lpercifield/visualight/Hardware/dev/DIY/5Wled-mosfet.brd

## EAGLE design Hardware/dev/DIY/5Wled-mosfet.brd (2013-02-26)

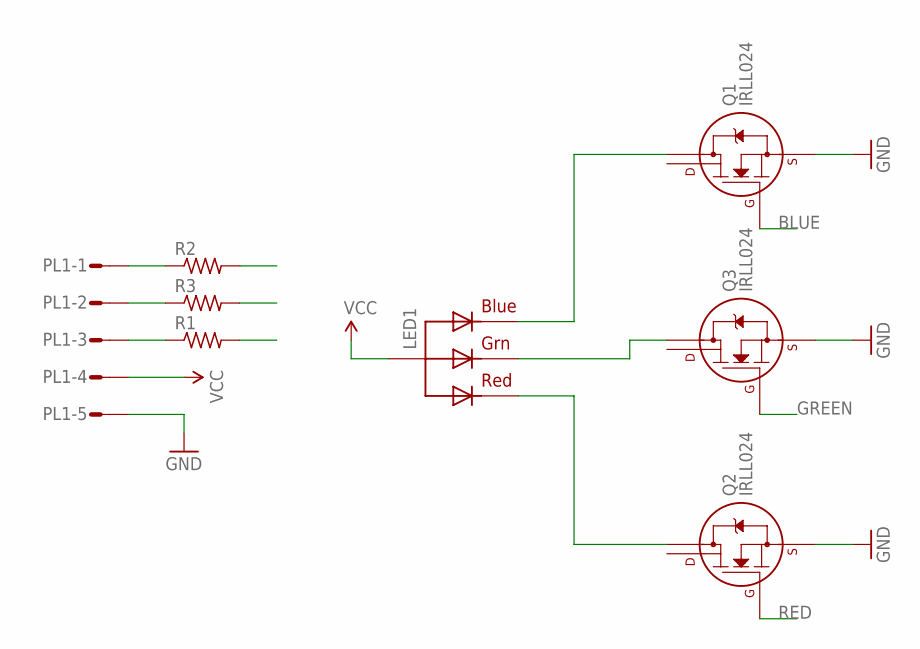
[picture p26: schematic 5Wled-mosfet.sch]

Parts:
LED1: RGBLED_CA4.5MM; 5WRGBLED
PL1: DF3-05R; DF3R-05
Q1, Q2, Q3: IRLL024; SOT-223
R1, R2, R3: R-US_0204/5; 0204/5

Connections:
BLUE: Q1.1 (G), R1.2
GND: PL1.5, Q1.3 (S), Q2.3 (S), Q3.3 (S)
GREEN: Q3.1 (G), R3.2
unnamed: LED1.1 (BLUE), Q1.2 (D1)
unnamed: LED1.3 (GREEN), Q3.2 (D1)
unnamed: LED1.2 (RED), Q2.2 (D1)
unnamed: PL1.1, R2.1
unnamed: PL1.2, R3.1
unnamed: PL1.3, R1.1
RED: Q2.1 (G), R2.2
VCC: LED1.4 (VCC), PL1.4

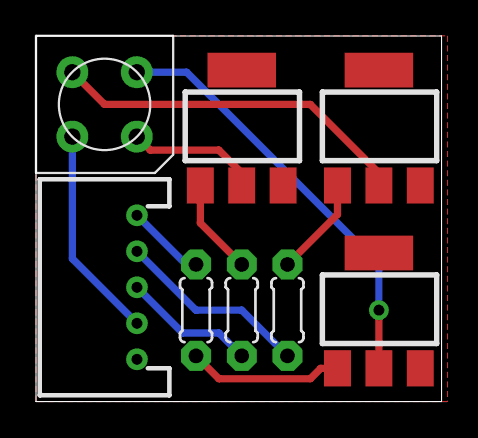
[picture p27: board 5Wled-mosfet.brd from above]

Board: 2 copper layers, 22.5 x 20.3 mm, 8 parts (0 on the bottom side), 11 nets.
