lpercifield/visualight/Hardware/dev/bulb/LEDdriverSFE_CREE.brd

## EAGLE design Hardware/dev/bulb/LEDdriverSFE_CREE.brd (2013-09-26)

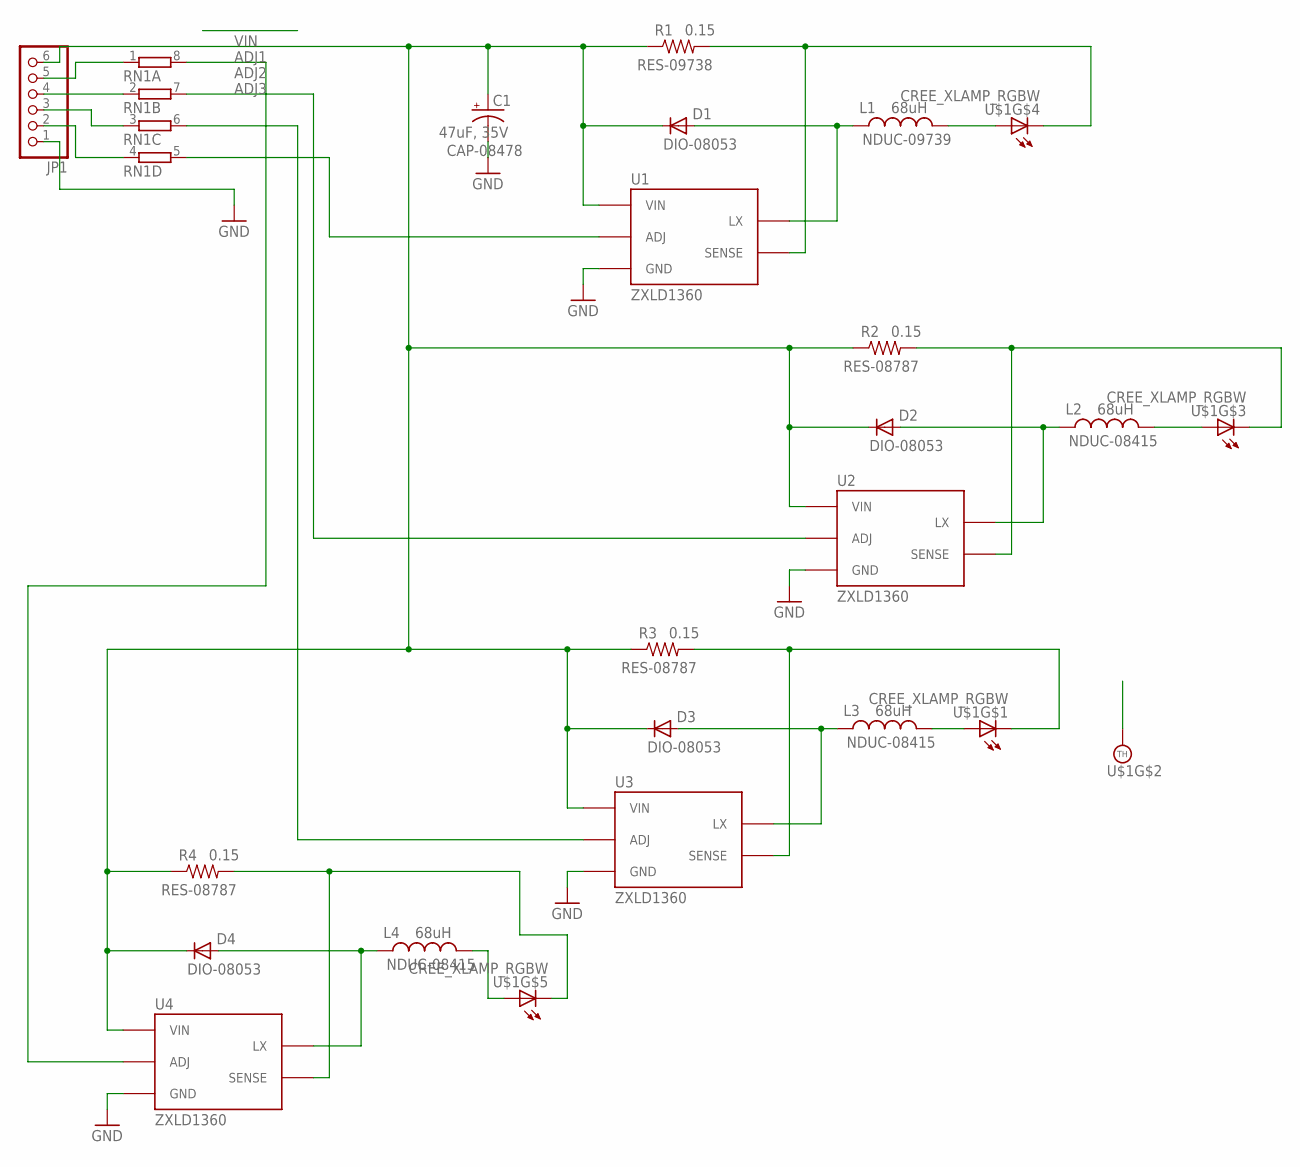
[picture p28: schematic LEDdriverSFE_CREE.sch]

Parts:
C1: 47uF, 35V; PANASONIC_D
D1, D2, D3, D4: MBRA140; SMA-DIODE
JP1: PINHD-1X6; 1X06
L1, L2, L3, L4: 68uH; CR75
R1, R2, R3, R4: 0.15; 0603-RES
RN1: 4R-NEXBV8V; EXBV8V
U1, U2, U3, U4: ZXLD1360; SOT23-5
U$1: CREE_XLAMP_RGBW; CREE_XLAMP_XML

Connections:
ADJ1: RN1.5 (2), U1.3 (ADJ)
ADJ2: RN1.7 (2), U2.3 (ADJ)
ADJ3: RN1.6 (2), U3.3 (ADJ)
GND: C1.-, JP1.1, U1.2 (GND), U2.2 (GND), U3.2 (GND), U4.2 (GND)
unnamed: L1.P$2 (2), U$1.3 (A)
unnamed: D2.A, L2.P$1 (1), U2.1 (LX)
unnamed: R2.2, U2.4 (SENSE), U$1.7 (C)
unnamed: D1.A, L1.P$1 (1), U1.1 (LX)
unnamed: R1.2, U1.4 (SENSE), U$1.6 (C)
unnamed: L2.P$2 (2), U$1.2 (A)
unnamed: D3.A, L3.P$1 (1), U3.1 (LX)
unnamed: R3.2, U3.4 (SENSE), U$1.8 (C)
unnamed: L3.P$2 (2), U$1.1 (A)
unnamed: D4.A, L4.P$1 (1), U4.1 (LX)
unnamed: R4.2, U4.4 (SENSE), U$1.5 (C)
unnamed: RN1.8 (2), U4.3 (ADJ)
unnamed: JP1.2, RN1.4 (1)
unnamed: JP1.5, RN1.1
unnamed: L4.P$2 (2), U$1.4 (A)
unnamed: JP1.4, RN1.2 (1)
unnamed: JP1.3, RN1.3 (1)
THERM: U$1.P$1 (TH)
VIN: C1.+, D1.C, D2.C, D3.C, D4.C, JP1.6, R1.1, R2.1, R3.1, R4.1, U1.5 (VIN), U2.5 (VIN), U3.5 (VIN), U4.5 (VIN)

Notes on the sheet:
NDUC-09739
RES-09738
CAP-08478
DIO-08053
NDUC-08415
RES-08787

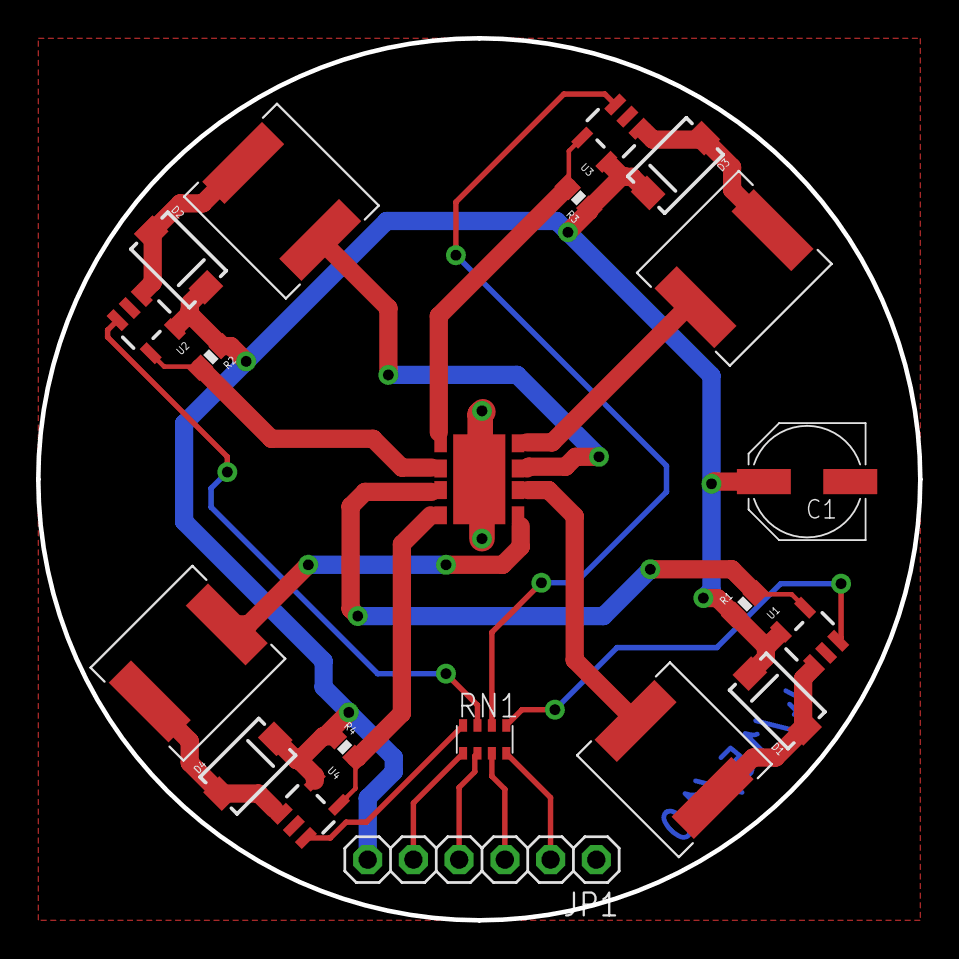
[picture p29: board LEDdriverSFE_CREE.brd from above]

Board: 2 copper layers, 49.0 x 49.0 mm, 20 parts (0 on the bottom side), 22 nets.
