lpercifield/visualight/Hardware/dev/DIY/5Wled-mosfet_2.brd

## EAGLE design Hardware/dev/DIY/5Wled-mosfet_2.brd (2013-02-26)

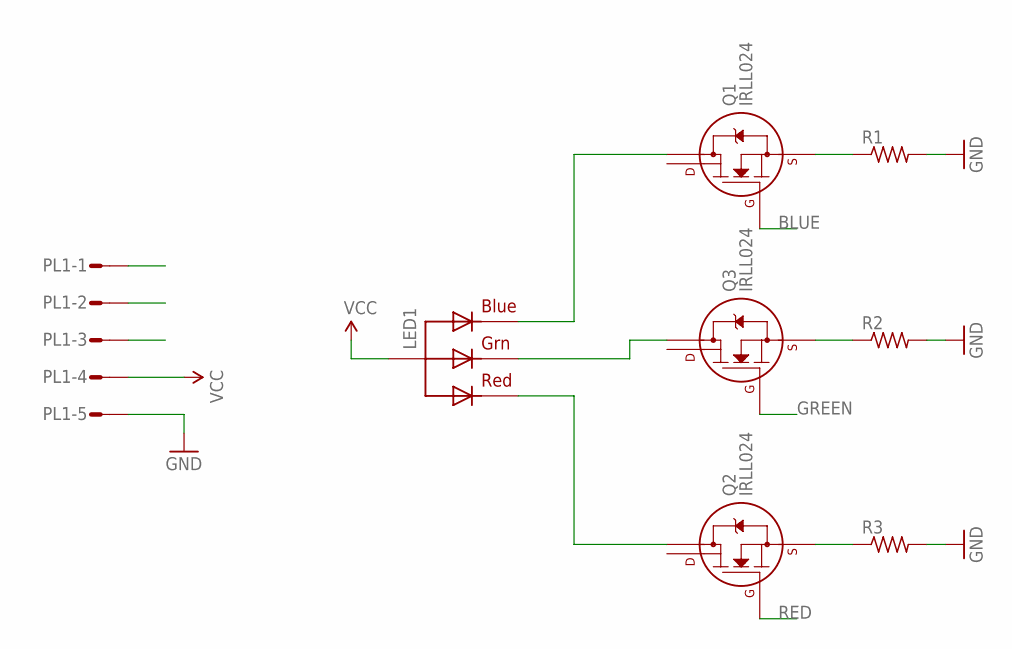
[picture p30: schematic 5Wled-mosfet_2.sch]

Parts:
LED1: RGBLED_CA4.5MM; 5WRGBLED
PL1: DF3-05R; DF3R-05
Q1, Q2, Q3: IRLL024; SOT-223
R1, R2, R3: R-US_0207/7; 0207/7

Connections:
BLUE: PL1.1, Q1.1 (G)
GND: PL1.5, R1.2, R2.2, R3.2
GREEN: PL1.2, Q3.1 (G)
unnamed: LED1.1 (BLUE), Q1.2 (D1)
unnamed: LED1.3 (GREEN), Q3.2 (D1)
unnamed: LED1.2 (RED), Q2.2 (D1)
unnamed: Q1.3 (S), R1.1
unnamed: Q3.3 (S), R2.1
unnamed: Q2.3 (S), R3.1
RED: PL1.3, Q2.1 (G)
VCC: LED1.4 (VCC), PL1.4

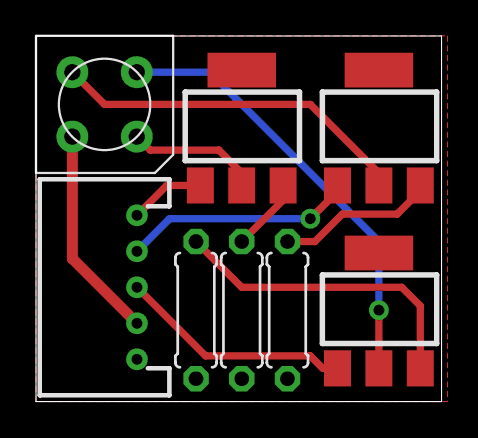
[picture p31: board 5Wled-mosfet_2.brd from above]

Board: 2 copper layers, 22.5 x 20.3 mm, 8 parts (0 on the bottom side), 11 nets.
