lpercifield/visualight/Hardware/dev/bulb/LEDdriverSFE.brd

## EAGLE design Hardware/dev/bulb/LEDdriverSFE.brd (2013-09-26)

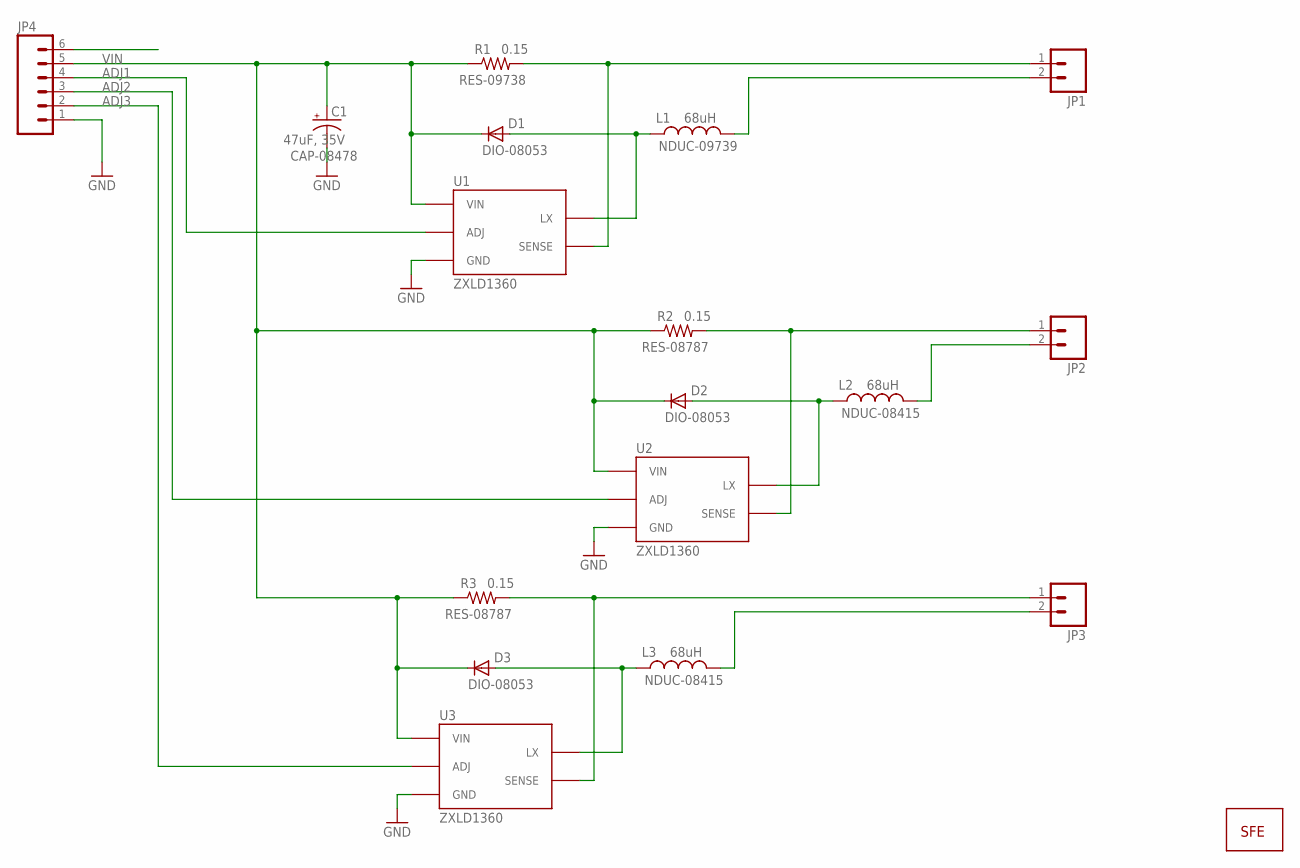
[picture p32: schematic LEDdriverSFE.sch]

Parts:
C1: 47uF, 35V; PANASONIC_D
D1, D2, D3: MBRA140; SMA-DIODE
JP1, JP2, JP3: M02; 1X02_LONGPADS
JP4: M06SIP; 1X06
JP5: LOGO-SFENEW; SFE-NEW-WEBLOGO
L1, L2, L3: 68uH; CR75
R1, R2, R3: 0.15; 0603-RES
U1, U2, U3: ZXLD1360; SOT23-5

Connections:
ADJ1: JP4.4, U1.3 (ADJ)
ADJ2: JP4.3, U2.3 (ADJ)
ADJ3: JP4.2, U3.3 (ADJ)
GND: C1.-, JP4.1, U1.2 (GND), U2.2 (GND), U3.2 (GND)
unnamed: JP1.2, L1.P$2 (2)
unnamed: D2.A, L2.P$1 (1), U2.1 (LX)
unnamed: JP2.1, R2.2, U2.4 (SENSE)
unnamed: D1.A, L1.P$1 (1), U1.1 (LX)
unnamed: JP1.1, R1.2, U1.4 (SENSE)
unnamed: JP2.2, L2.P$2 (2)
unnamed: D3.A, L3.P$1 (1), U3.1 (LX)
unnamed: JP3.1, R3.2, U3.4 (SENSE)
unnamed: JP3.2, L3.P$2 (2)
VIN: C1.+, D1.C, D2.C, D3.C, JP4.5, R1.1, R2.1, R3.1, U1.5 (VIN), U2.5 (VIN), U3.5 (VIN)

Notes on the sheet:
NDUC-09739
RES-09738
CAP-08478
DIO-08053
NDUC-08415
RES-08787

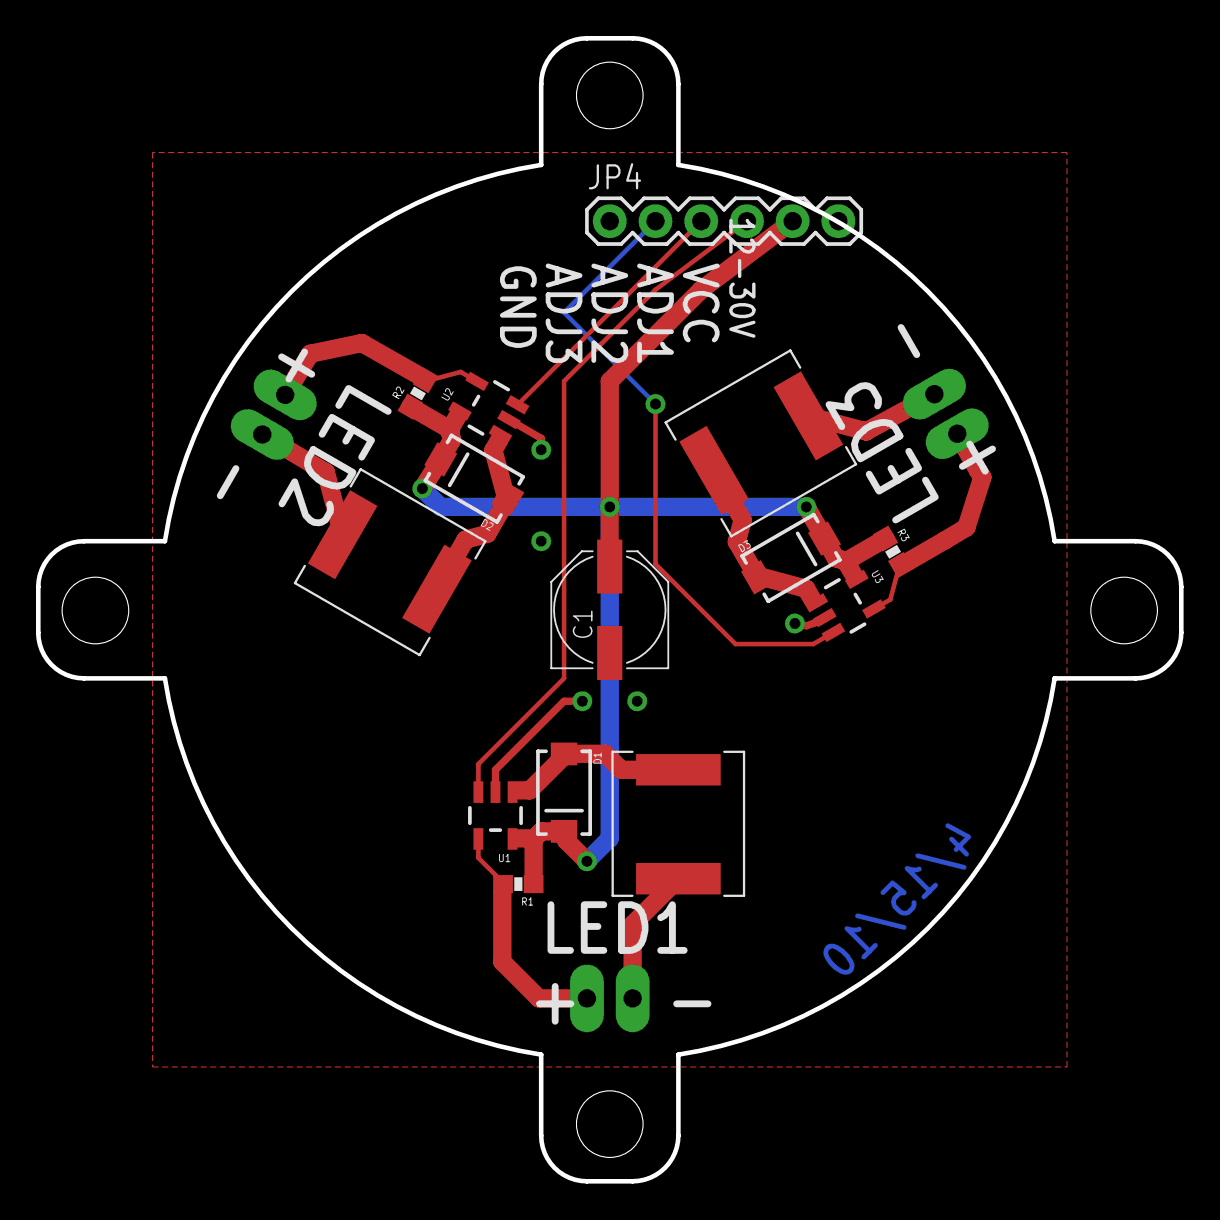
[picture p33: board LEDdriverSFE.brd from above]

Board: 2 copper layers, 63.5 x 63.5 mm, 18 parts (1 on the bottom side), 14 nets.
