lpercifield/visualight/Hardware/dev/bulb/LED.brd

## EAGLE design Hardware/dev/bulb/LED.brd (2013-02-26)

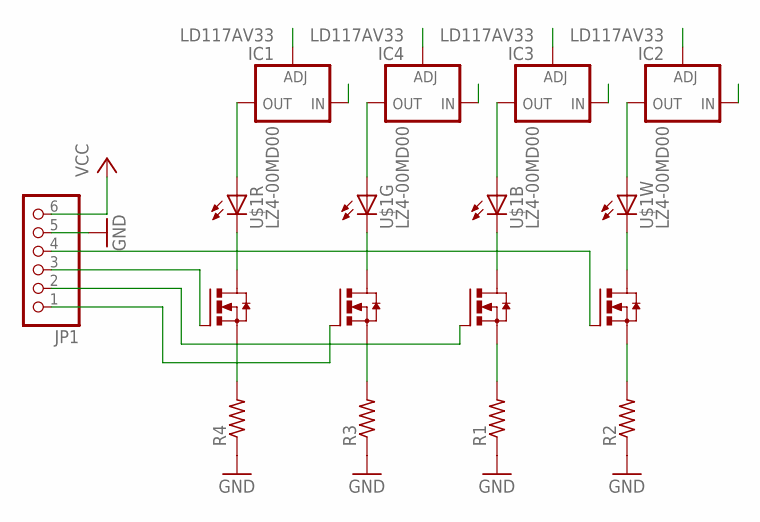
[picture p34: schematic LED.sch]

Parts:
IC1, IC2, IC3, IC4: LD117AV33; TO220L1
JP1: PINHD-1X6; 1X06
Q1, Q2, Q3, Q4: N-HEXFET_SOT323-; SOT223
R1, R2, R3, R4: R-US_0204/7; 0204/7
U$1: LZ4-00MD00; LZ4-00MD0

Connections:
BLUE: JP1.2, Q1.1 (G)
GND: IC1.1 (ADJ), IC2.1 (ADJ), IC3.1 (ADJ), IC4.1 (ADJ), JP1.5, R1.1, R2.1, R3.1, R4.1
GREEN: JP1.1, Q2.1 (G)
unnamed: Q2.3 (S), R3.2
unnamed: Q3.3 (S), R4.2
unnamed: Q1.3 (S), R1.2
unnamed: Q4.3 (S), R2.2
unnamed: Q3.4 (D), U$1.4 (C)
unnamed: Q2.4 (D), U$1.6 (C)
unnamed: Q1.4 (D), U$1.8 (C)
unnamed: Q4.4 (D), U$1.2 (C)
unnamed: IC2.2 (OUT), U$1.1 (A)
unnamed: IC3.2 (OUT), U$1.7 (A)
unnamed: IC4.2 (OUT), U$1.5 (A)
unnamed: IC1.2 (OUT), U$1.3 (A)
RED: JP1.3, Q3.1 (G)
VCC: IC1.3 (IN), IC2.3 (IN), IC3.3 (IN), IC4.3 (IN), JP1.6
WHITE: JP1.4, Q4.1 (G)

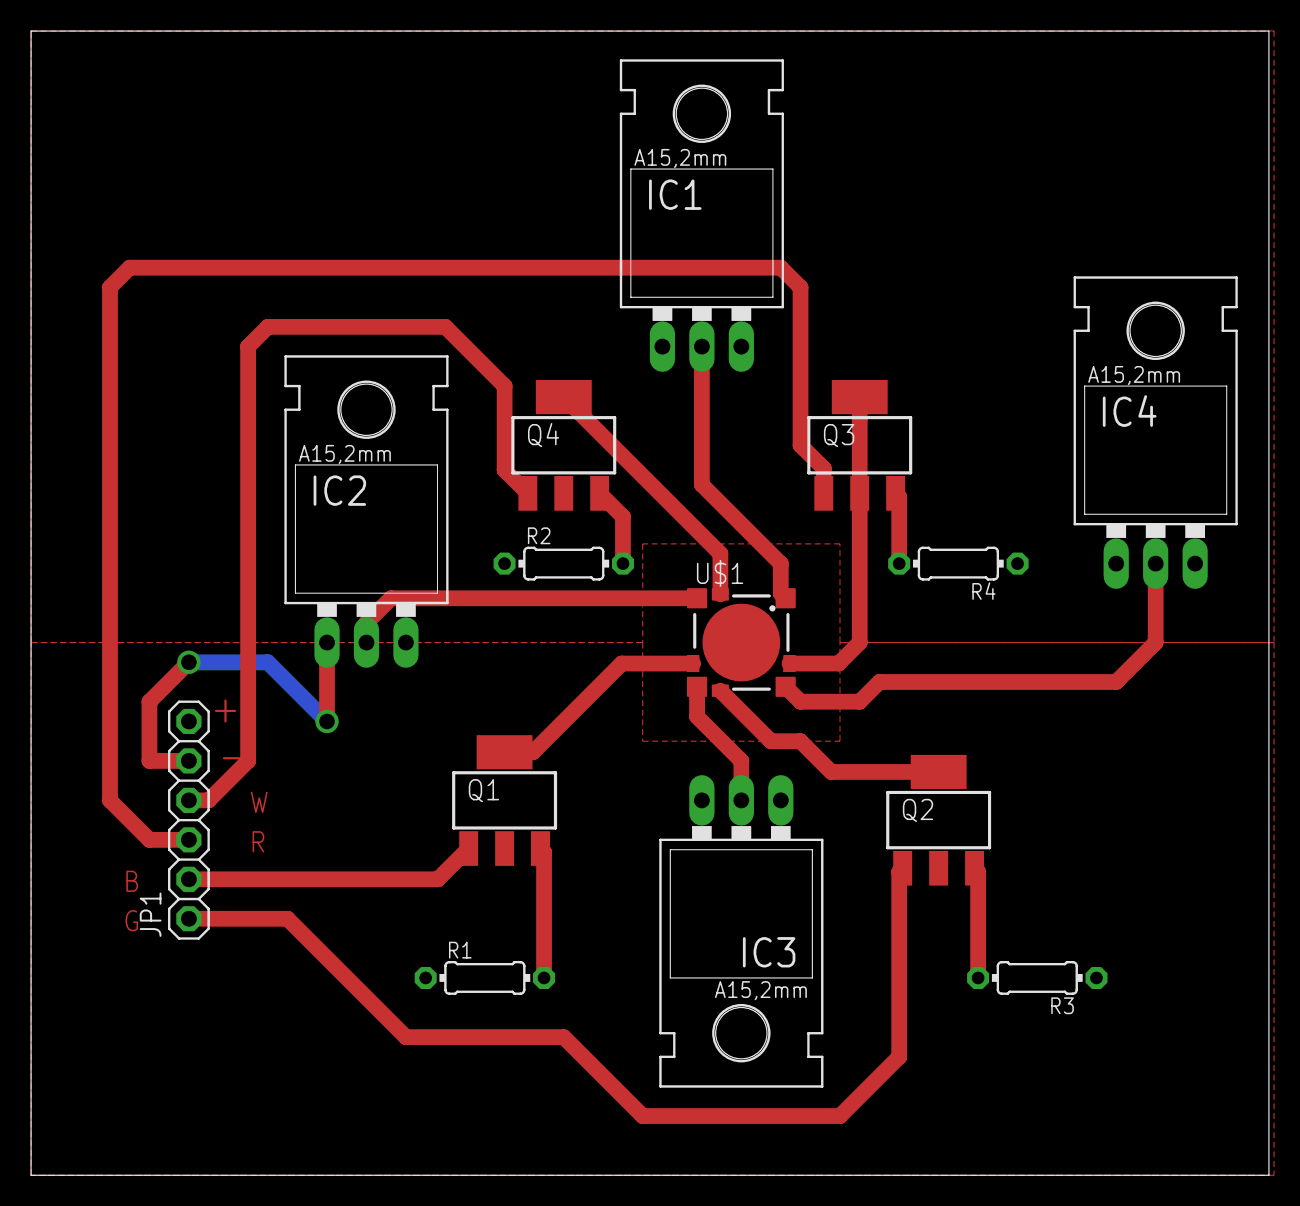
[picture p35: board LED.brd from above]

Board: 2 copper layers, 79.7 x 73.7 mm, 14 parts (0 on the bottom side), 18 nets.
